smartboxchannel/EFEKTA-EINK154-TEMP-HUM-PRES-SENSOR-NRF52_V3/Images/PCB_154v3T_A.png

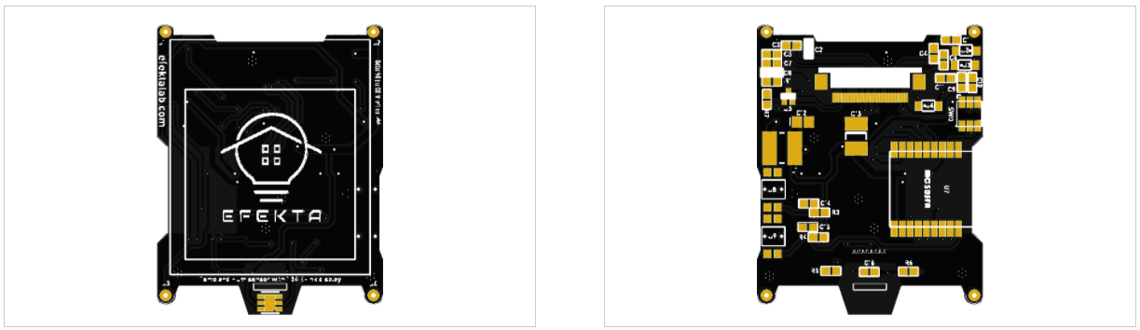
Images/PCB_154v3T_A.png
