smartboxchannel/EFEKTA-EINK154-TEMP-HUM-PRES-SENSOR-NRF52_V3/CODE/Arduino/TH/eink54imagedata.cpp

// ######################  Temperature and humidity sensor with electronic ink display 1.54 | nRF52 ####################### //
//                                                                                                                          //
//        @filename   :   EFEKTA_THEINK154_1.8.ino                                                                          //
//        @brief en   :   Wireless, battery-operated temperature and humidity sensor (SHT20, SI7020)                        //
//                        with electronic ink display(good display). Works on nRF52.                                        //
//        @brief ru   :   Беcпроводной, батарейный датчик температуры и влажности(sht20, si7020)                            //
//                        с дисплеем на электронных чернилах(good display). Работает на nRF52.                              //
//        @author     :   Andrew Lamchenko aka Berk                                                                         //
//                                                                                                                          //
//        Copyright (C) EFEKTALAB 2020                                                                                      //
//                                                                                                                          //
//        Copyright (C) Waveshare     September 5 2017                                                                      //
//                                                                                                                          //
// ######################################################################################################################## //

#include "eink54imagedata.h"
#include <avr/pgmspace.h>

const unsigned char IMAGE_DATA2[1573] PROGMEM = { /* 0X01,0X01,0X79,0X00,0X64,0X00, */
0X00,0X00,0X00,0X00,0X00,0X00,0X00,0X00,0X00,0X00,0X00,0X00,0X00,0X00,0X00,0X00,
0X00,0X00,0X00,0X00,0X00,0X00,0X00,0X00,0X00,0X00,0X00,0X00,0X00,0X00,0X00,0X00,
0X00,0X00,0X00,0X00,0X00,0X00,0X00,0X00,0X00,0X00,0X00,0X00,0X00,0X00,0X00,0X00,
0X00,0X00,0X00,0X00,0X00,0X00,0X1F,0XFF,0XFF,0XFF,0XFF,0XFF,0XFF,0XFF,0X80,0X00,
0X00,0X00,0X00,0X30,0X00,0X00,0X00,0X00,0X00,0X00,0X00,0XC0,0X00,0X00,0X00,0X00,
0X60,0X00,0X00,0X00,0X00,0X00,0X00,0X01,0XE0,0X00,0X00,0X00,0X00,0X40,0X00,0X00,
0X00,0X00,0X00,0X00,0X01,0XF0,0X00,0X00,0X00,0X00,0X80,0X00,0X00,0X00,0X00,0X00,
0X00,0X03,0XF0,0X00,0X00,0X00,0X00,0X80,0X00,0X00,0X00,0X00,0X00,0X00,0X03,0XF8,
0X00,0X00,0X00,0X01,0X00,0X00,0X00,0X00,0X00,0X00,0X00,0X07,0XF8,0X00,0X00,0X00,
0X03,0X00,0X00,0X00,0X00,0X00,0X00,0X00,0X07,0XFC,0X00,0X00,0X00,0X02,0X00,0X00,
0X00,0X00,0X00,0X00,0X00,0X0F,0XFE,0X00,0X00,0X00,0X06,0X00,0X00,0X00,0X00,0X00,
0X00,0X00,0X1F,0XFE,0X00,0X00,0X00,0X04,0X00,0X00,0X00,0X00,0X00,0X00,0X00,0X1F,
0XFF,0X00,0X00,0X00,0X0C,0X00,0X00,0X00,0X00,0X00,0X00,0X00,0X3F,0XFF,0X80,0X00,
0X00,0X08,0X00,0X00,0X00,0X00,0X00,0X00,0X00,0X3F,0XFF,0X80,0X00,0X00,0X18,0X00,
0X00,0X00,0X00,0X00,0X00,0X00,0X7F,0XFF,0XC0,0X00,0X00,0X30,0X00,0X00,0X00,0X00,
0X00,0X00,0X00,0X7F,0XFF,0XE0,0X00,0X00,0X20,0X00,0X00,0X00,0X00,0X00,0X00,0X00,
0XFF,0XFF,0XE0,0X00,0X00,0X60,0X00,0X00,0X00,0X00,0X00,0X00,0X01,0XFF,0XFF,0XF0,
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
0X00,0X00,0X00,0X00,0X00,0X00,0X00,0X00,0X00,0X00,0X00,0X00,0X00,0X00,0X00,0X00,
0X00,0X00,0X00,0X00,0X00,0X00,0X00,0X00,0X00,0X00,0X00,0X00,0X00,0X00,0X00,0X00,
0X00,0X00,0X00,0X00,0X00,0X00,0X00,0X00,0X00,0X00,0X00,0X00,0X00,0X00,0X00,0X00,
0X00,0X00,0X00,0X00,};
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
