smartboxchannel/EFEKTA-EINK154-TEMP-HUM-PRES-SENSOR-NRF52_V3/CODE/Arduino/TH/eink54.h

// ######################  Temperature and humidity sensor with electronic ink display 1.54 | nRF52 ####################### //
//                                                                                                                          //
//        @filename   :   EFEKTA_THEINK154_1.8.ino                                                                          //
//        @brief en   :   Wireless, battery-operated temperature and humidity sensor (SHT20, SI7020)                        //
//                        with electronic ink display(good display). Works on nRF52.                                        //
//        @brief ru   :   Беcпроводной, батарейный датчик температуры и влажности(sht20, si7020)                            //
//                        с дисплеем на электронных чернилах(good display). Работает на nRF52.                              //
//        @author     :   Andrew Lamchenko aka Berk                                                                         //
//                                                                                                                          //
//        Copyright (C) EFEKTALAB 2020                                                                                      //
//                                                                                                                          //
//        Copyright (C) Waveshare     September 5 2017                                                                      //
//                                                                                                                          //
// ######################################################################################################################## //

#ifndef EPD1IN54_H
#define EPD1IN54_H

#include "eink54if.h"

// Display resolution
#define EPD_WIDTH       200
#define EPD_HEIGHT      200

// EPD1IN54 commands
#define DRIVER_OUTPUT_CONTROL                       0x01
#define BOOSTER_SOFT_START_CONTROL                  0x0C
#define GATE_SCAN_START_POSITION                    0x0F
#define DEEP_SLEEP_MODE                             0x10
#define DATA_ENTRY_MODE_SETTING                     0x11
#define SW_RESET                                    0x12
#define TEMPERATURE_SENSOR_CONTROL                  0x1A
#define MASTER_ACTIVATION                           0x20
#define DISPLAY_UPDATE_CONTROL_1                    0x21
#define DISPLAY_UPDATE_CONTROL_2                    0x22
#define WRITE_RAM                                   0x24
#define WRITE_VCOM_REGISTER                         0x2C
#define WRITE_LUT_REGISTER                          0x32
#define SET_DUMMY_LINE_PERIOD                       0x3A
#define SET_GATE_TIME                               0x3B
#define BORDER_WAVEFORM_CONTROL                     0x3C
#define SET_RAM_X_ADDRESS_START_END_POSITION        0x44
#define SET_RAM_Y_ADDRESS_START_END_POSITION        0x45
#define SET_RAM_X_ADDRESS_COUNTER                   0x4E
#define SET_RAM_Y_ADDRESS_COUNTER                   0x4F
#define TERMINATE_FRAME_READ_WRITE                  0xFF

extern const unsigned char lut_full_update[];
extern const unsigned char lut_partial_update[];

class Epd : EpdIf {
public:
    unsigned long width;
    unsigned long height;

    Epd();
    ~Epd();
    int  Init(const unsigned char* lut);
    void SendCommand(unsigned char command);
    void SendData(unsigned char data);
    void WaitUntilIdle(void);
    void Reset(void);
    void SetFrameMemory(
        const unsigned char* image_buffer,
        int x,
        int y,
        int image_width,
        int image_height
    );
    void SetFrameMemory(const unsigned char* image_buffer);
    void ClearFrameMemory(unsigned char color);
    void DisplayFrame(void);
    void Sleep(void);

private:
    unsigned int reset_pin;
    unsigned int dc_pin;
    unsigned int cs_pin;
    unsigned int busy_pin;
    const unsigned char* lut;

    void SetLut(const unsigned char* lut);
    void SetMemoryArea(int x_start, int y_start, int x_end, int y_end);
    void SetMemoryPointer(int x, int y);
};

#endif /* EPD1IN54_H */

/* END OF FILE */
